FossTag/Tagger/docs/images/conversions/01-Grey/trigger-closeup.jpg

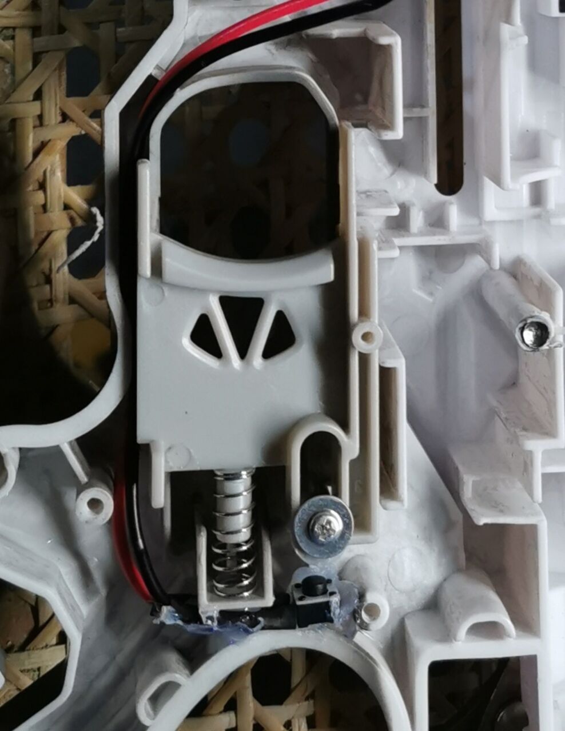
docs/images/conversions/01-Grey/trigger-closeup.jpg
