FossTag/Tagger/docs/images/pcbs/breadboard/breadboard-taggers-communicating.jpg

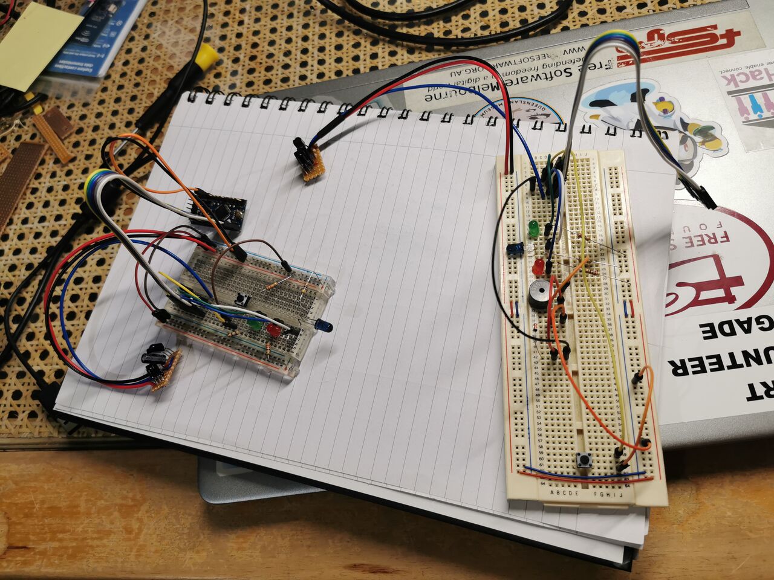
docs/images/pcbs/breadboard/breadboard-taggers-communicating.jpg
