FossTag/Tagger/docs/images/pcbs/prototype/Tagger-Prototype-bottom.jpg

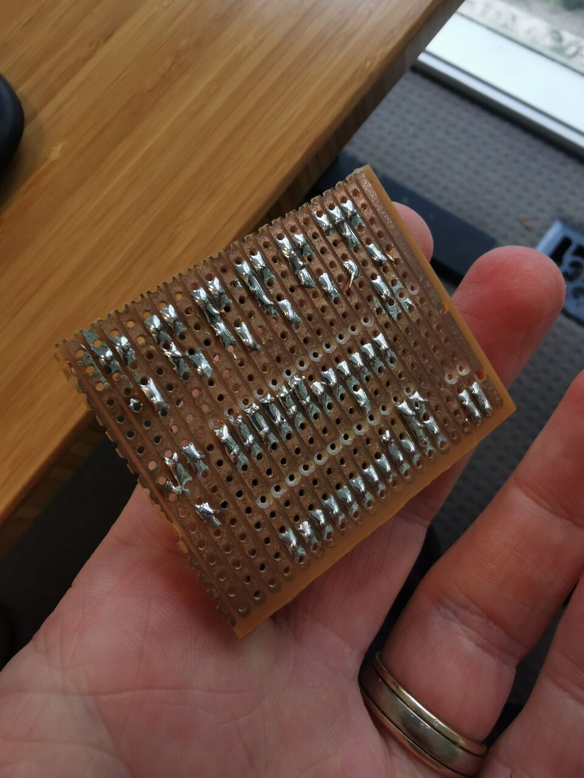
docs/images/pcbs/prototype/Tagger-Prototype-bottom.jpg
